Yun04kaGasai/Command-Case-1-Guidance-System-Module-2098/Assets/Diagramma dejstvij bloka posledovatel'nogo vypolneniya tipov skanirovaniya.png

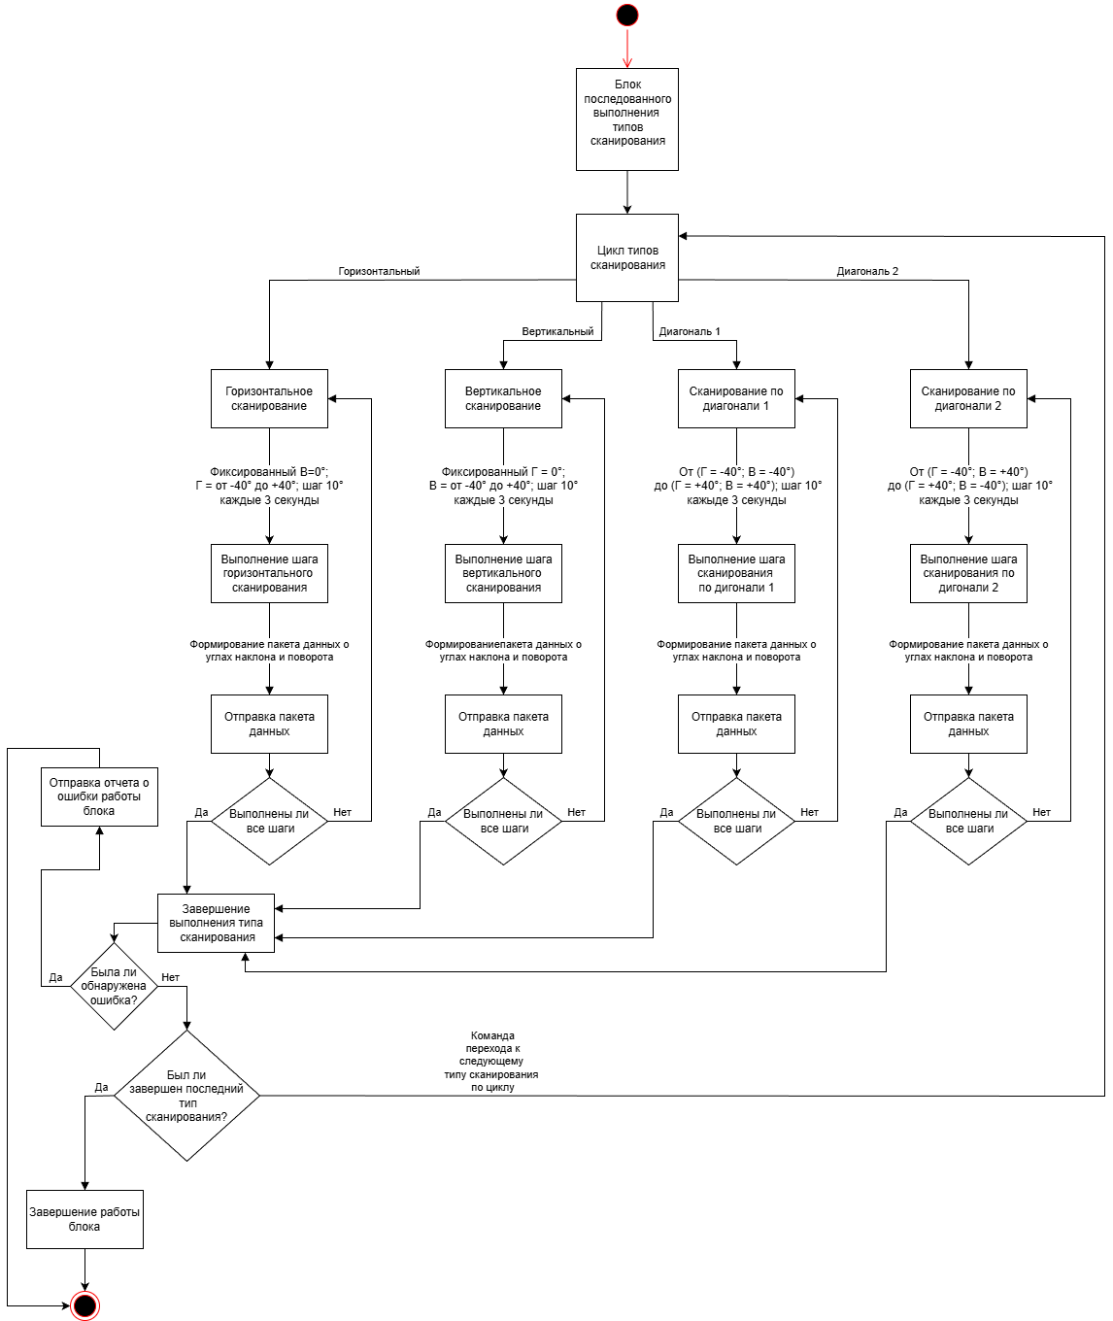
Assets/Diagramma dejstvij bloka posledovatel'nogo vypolneniya tipov skanirovaniya.png
