Yun04kaGasai/Command-Case-1-Guidance-System-Module-2098/Assets/Diagramma dejstvij CubeSat.png

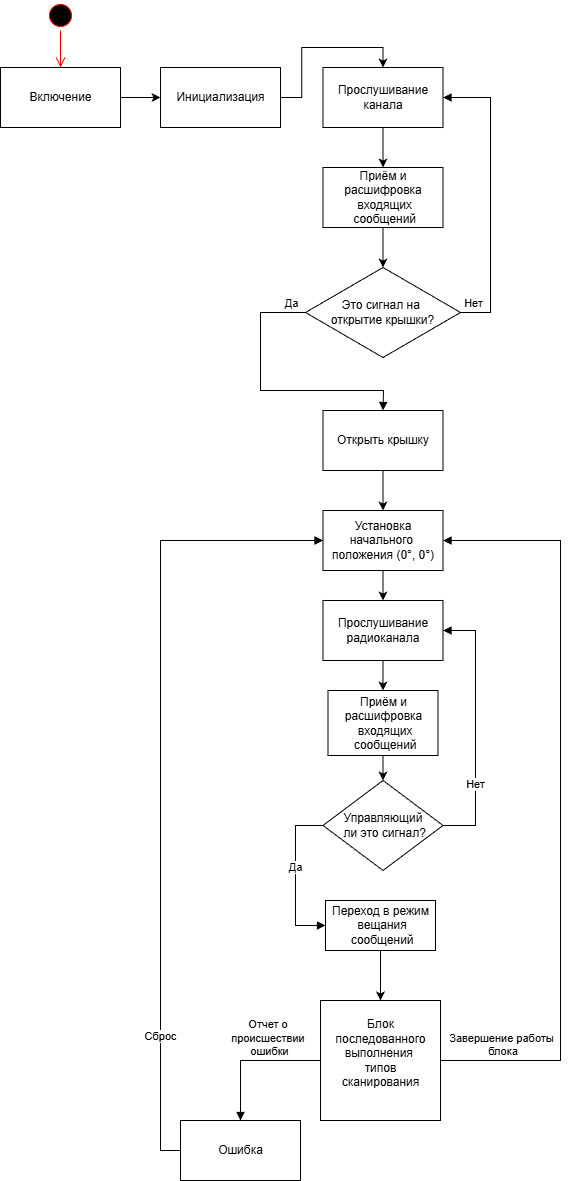
Assets/Diagramma dejstvij CubeSat.png
