Yun04kaGasai/Command-Case-1-Guidance-System-Module-2098/Assets/Diagramma klassov CubeSat.png

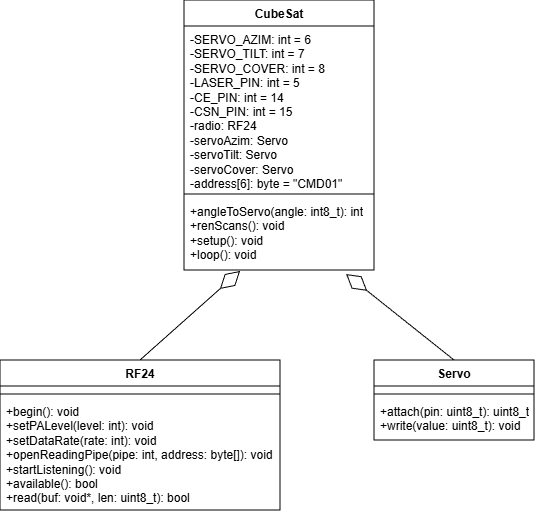
Assets/Diagramma klassov CubeSat.png
