Yun04kaGasai/Command-Case-1-Guidance-System-Module-2098/Assets/Diagramma klassov nazemnoj stancii.png

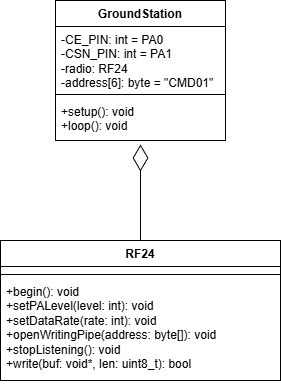
Assets/Diagramma klassov nazemnoj stancii.png
