Yun04kaGasai/Command-Case-1-Guidance-System-Module-2098/Assets/isometry razn.png

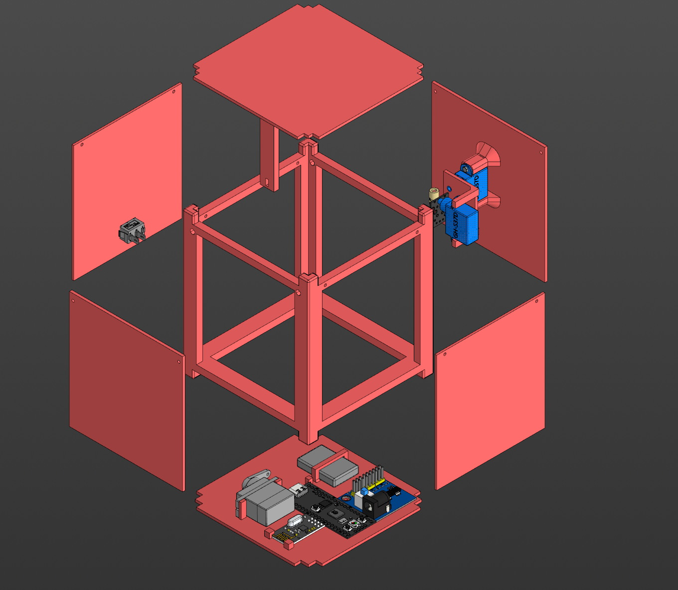
Assets/isometry razn.png
