Yun04kaGasai/Command-Case-1-Guidance-System-Module-2098/Assets/isometry.png

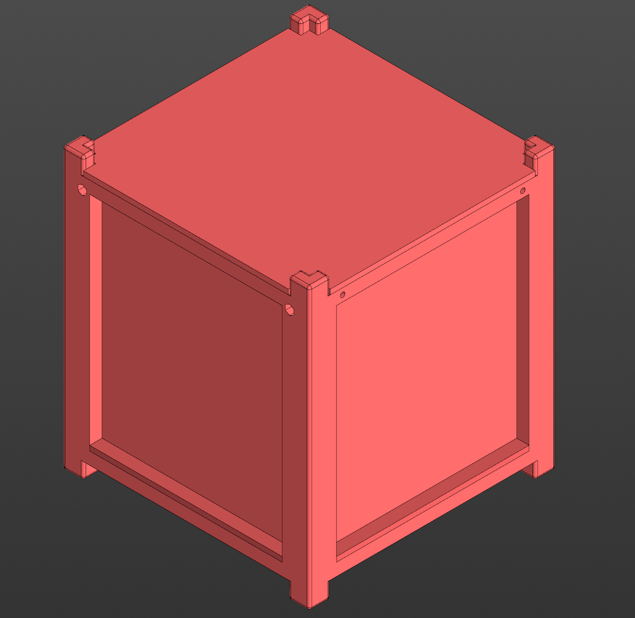
Assets/isometry.png
