Yun04kaGasai/Command-Case-1-Guidance-System-Module-2098/Assets/Potencial'naya skhema CubeSat.png

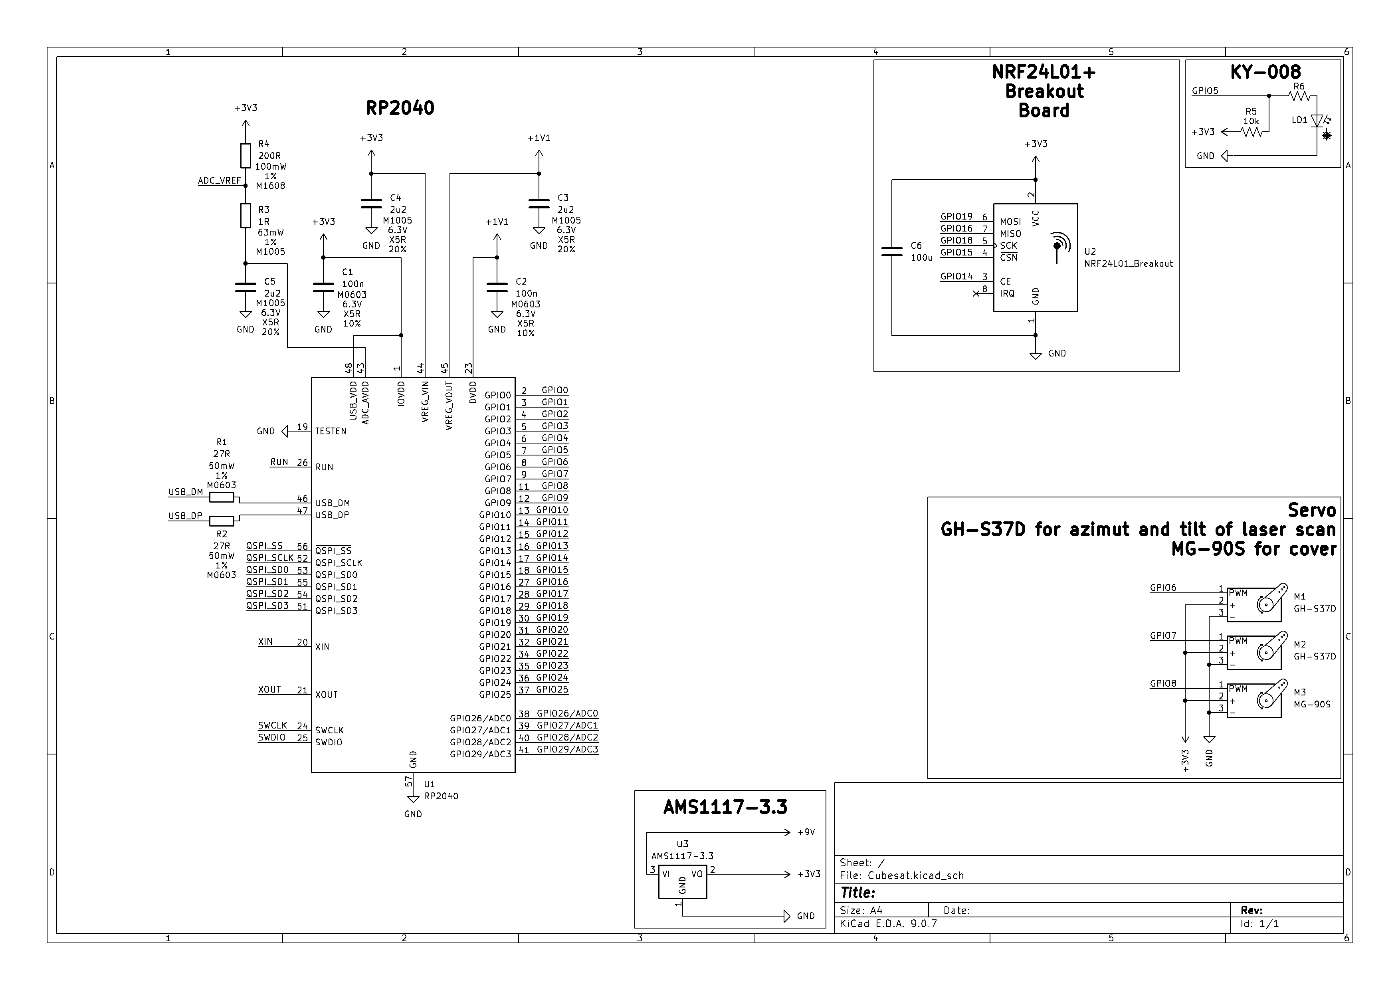
Assets/Potencial'naya skhema CubeSat.png
