Yun04kaGasai/Command-Case-1-Guidance-System-Module-2098/Assets/Potencial'naya skhema nazemnoj stancii.png

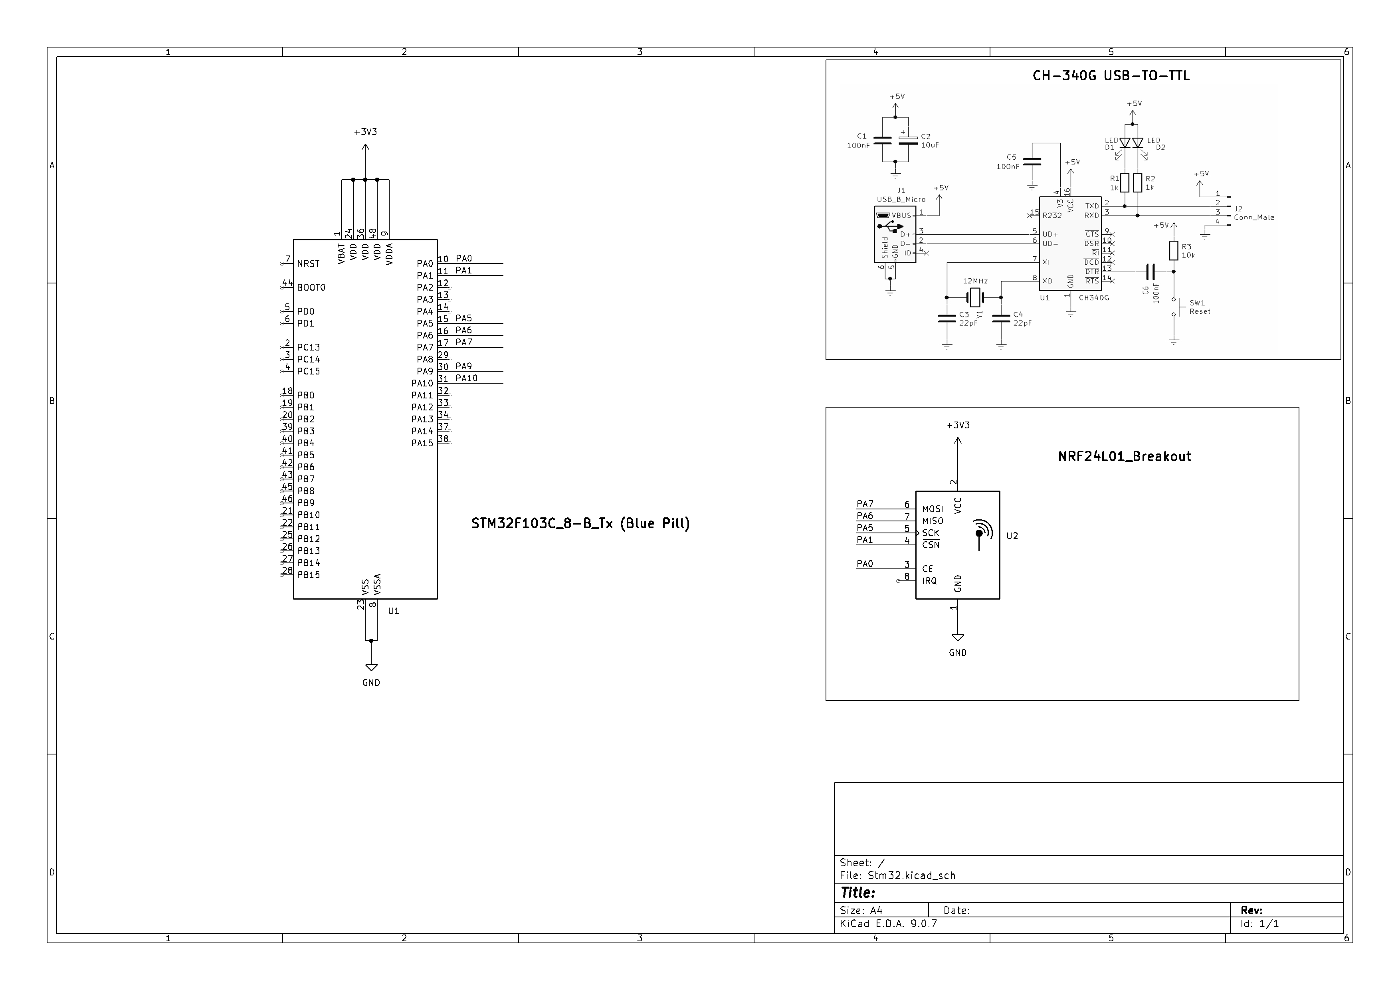
Assets/Potencial'naya skhema nazemnoj stancii.png
