Yun04kaGasai/Command-Case-1-Guidance-System-Module-2098/Assets/Сборка/Сборка.png

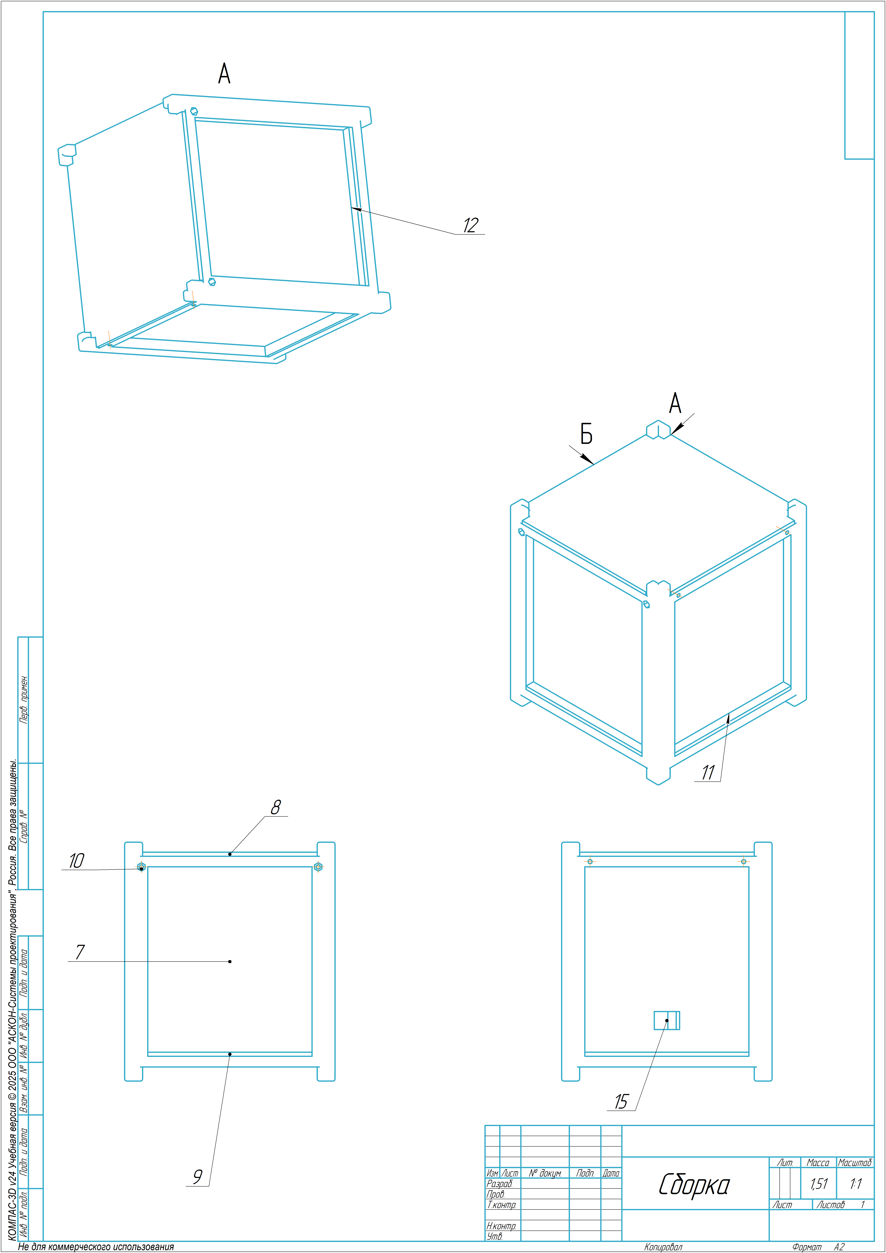
Assets/Сборка/Сборка.png
