Yun04kaGasai/Command-Case-1-Guidance-System-Module-2098/Assets/Чертежи/Дно кубсат.png

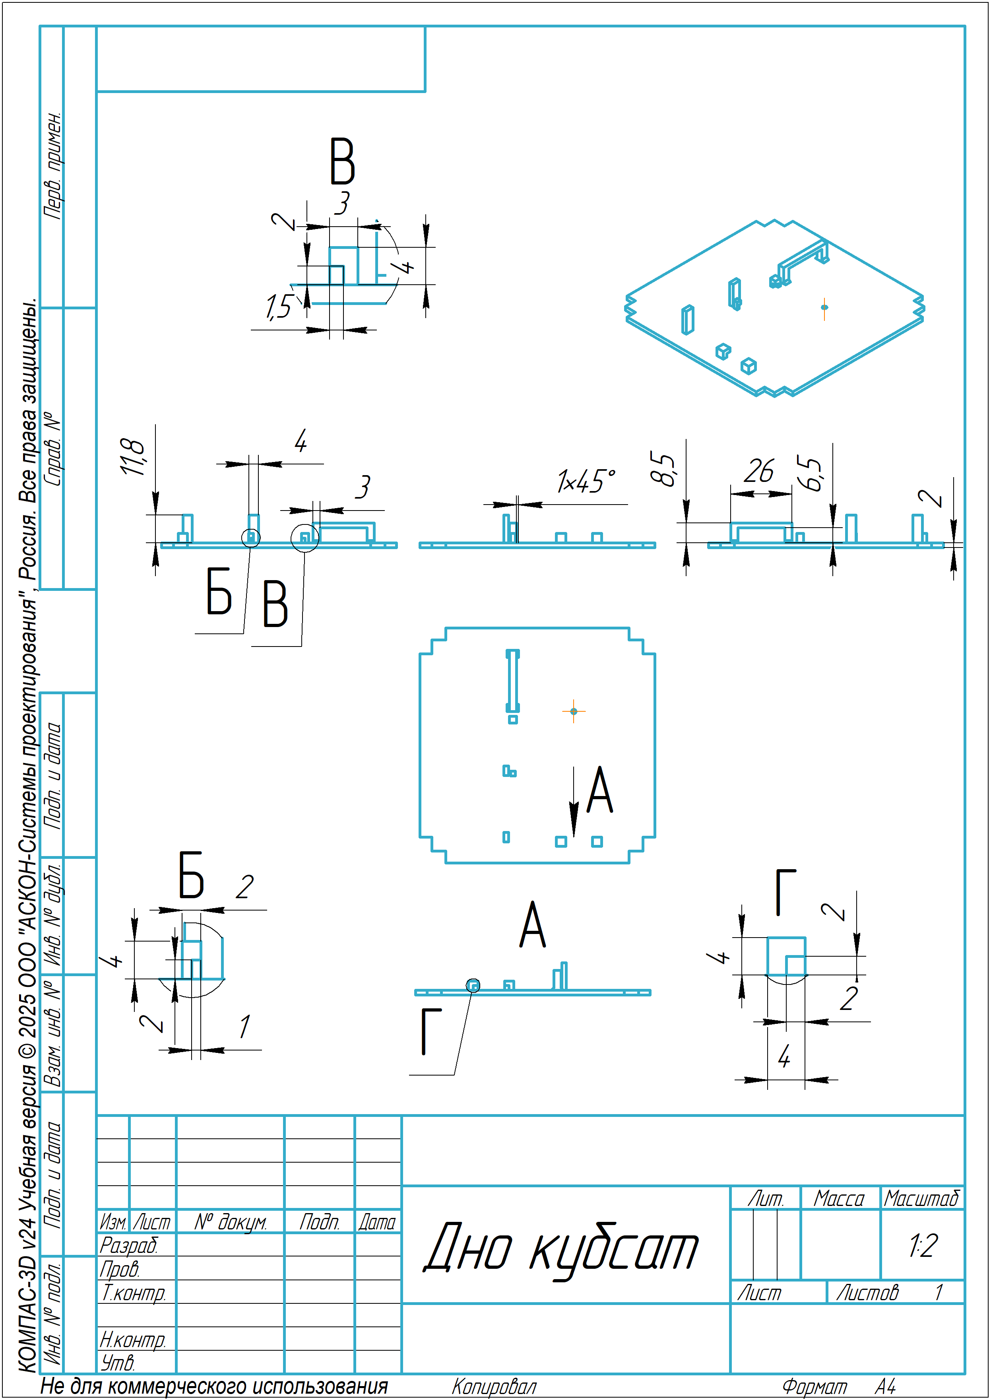
Assets/Чертежи/Дно кубсат.png
