Yun04kaGasai/Command-Case-1-Guidance-System-Module-2098/Assets/Чертежи/Крепление сервопривода.png

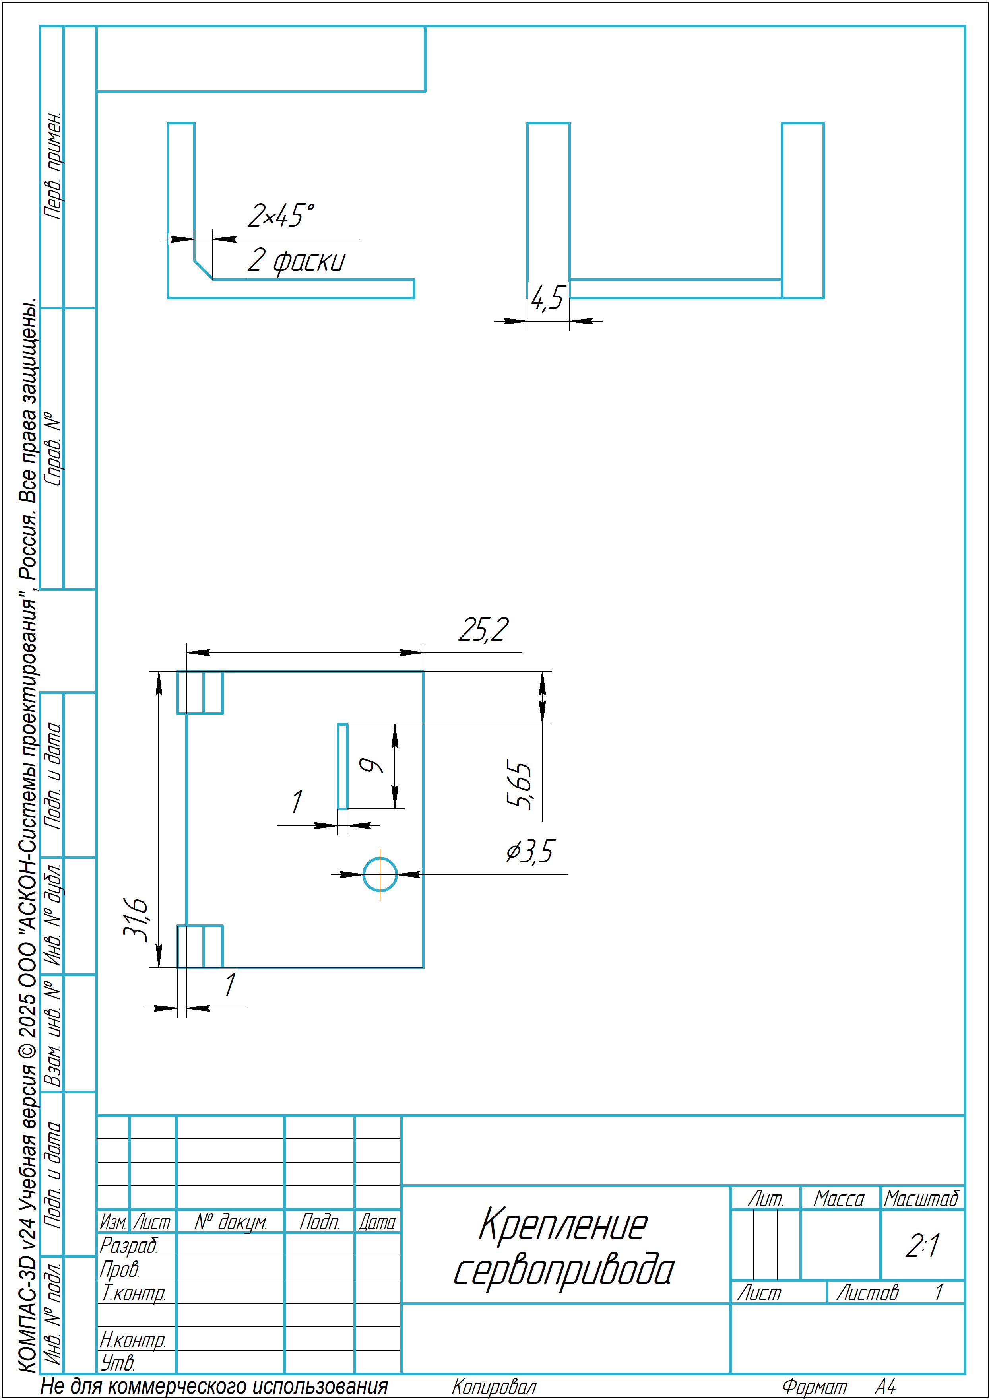
Assets/Чертежи/Крепление сервопривода.png
