Yun04kaGasai/Command-Case-1-Guidance-System-Module-2098/Assets/Чертежи/Стенка без крепления.png

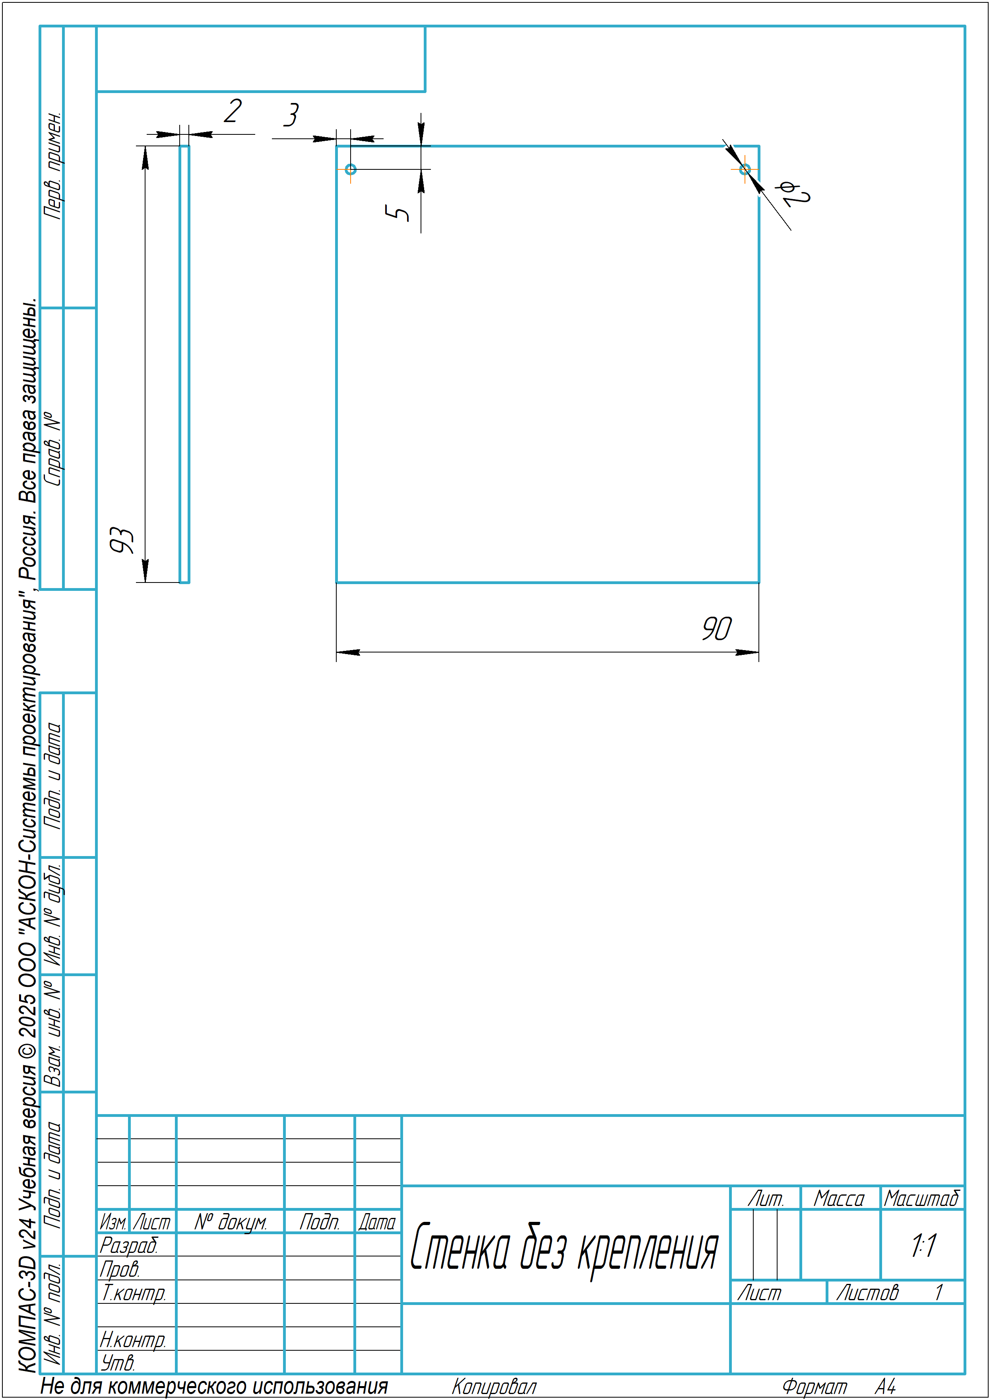
Assets/Чертежи/Стенка без крепления.png
