Yun04kaGasai/Command-Case-1-Guidance-System-Module-2098/Assets/Чертежи/Стенка_С_Креплением.png

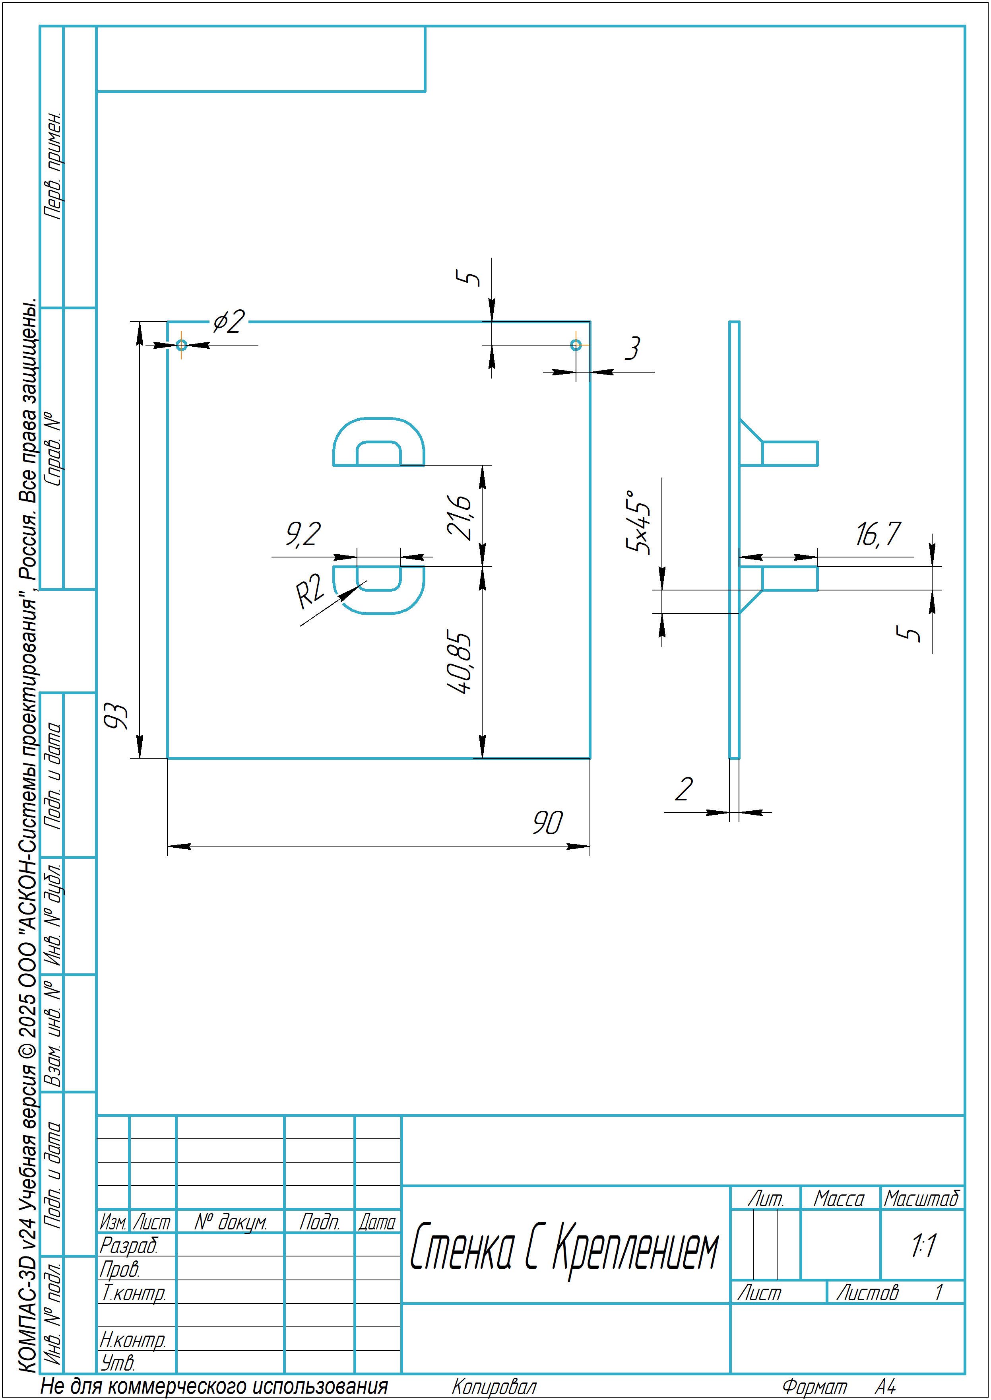
Assets/Чертежи/Стенка_С_Креплением.png
