Yun04kaGasai/Command-Case-1-Guidance-System-Module-2098/Assets/Сборка/RP2040/Rp2040 Type C.stl

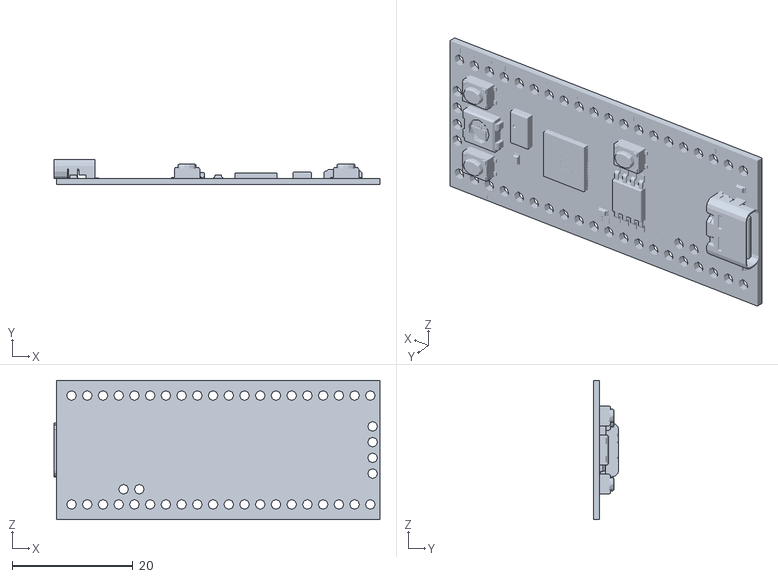
[picture p34: CAD file, 2026-01-14]
Assets/Сборка/RP2040/Rp2040 Type C.stl
53.9 x 4.19 x 23.0
