Yun04kaGasai/Command-Case-1-Guidance-System-Module-2098/Assets/Сборка/RadioFrequencyCommunicationModule_nRF24L01.STEP

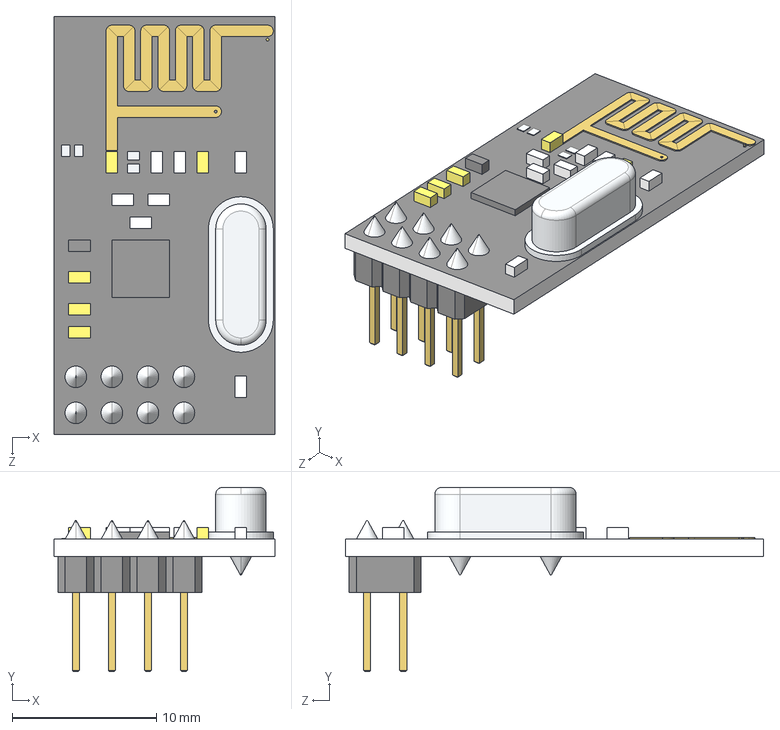
[picture p35: CAD file, 2026-01-14]
Assets/Сборка/RadioFrequencyCommunicationModule_nRF24L01.STEP
15.3 x 12.8 x 29.0 mm
