Yun04kaGasai/Command-Case-1-Guidance-System-Module-2098/Assets/Сборка/RP2040/C-Type Female - 6-Pin SMD.step

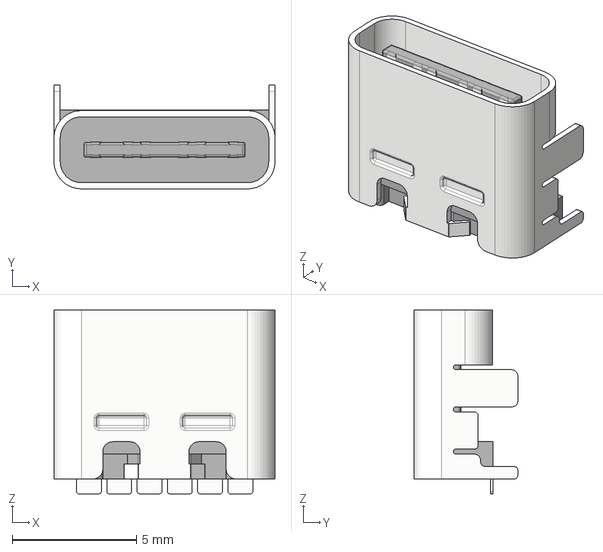
[picture p36: CAD file, 2026-01-14]
Assets/Сборка/RP2040/C-Type Female - 6-Pin SMD.step
8.90 x 4.18 x 7.40 mm
