Yun04kaGasai/Command-Case-1-Guidance-System-Module-2098/3D-модели/Крышка.stp

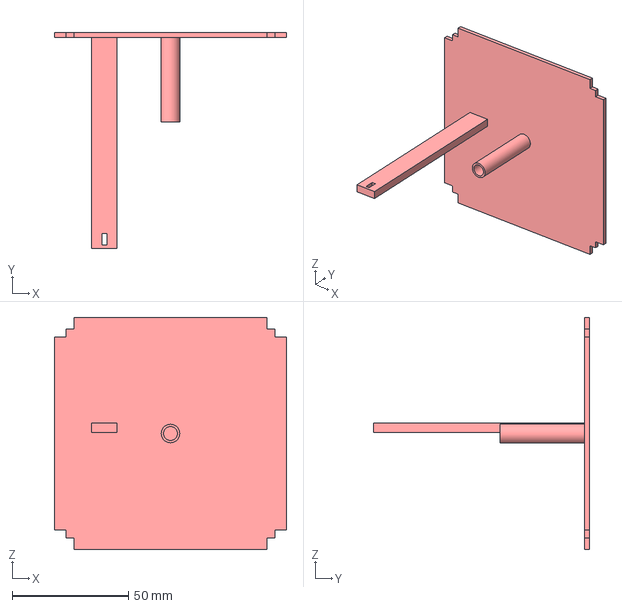
[picture p37: CAD file, 2026-01-18]
3D-модели/Крышка.stp
100.0 x 93.0 x 100.0 mm
