Yun04kaGasai/Command-Case-1-Guidance-System-Module-2098/Assets/Сборка/Сборка Кубсат.stp

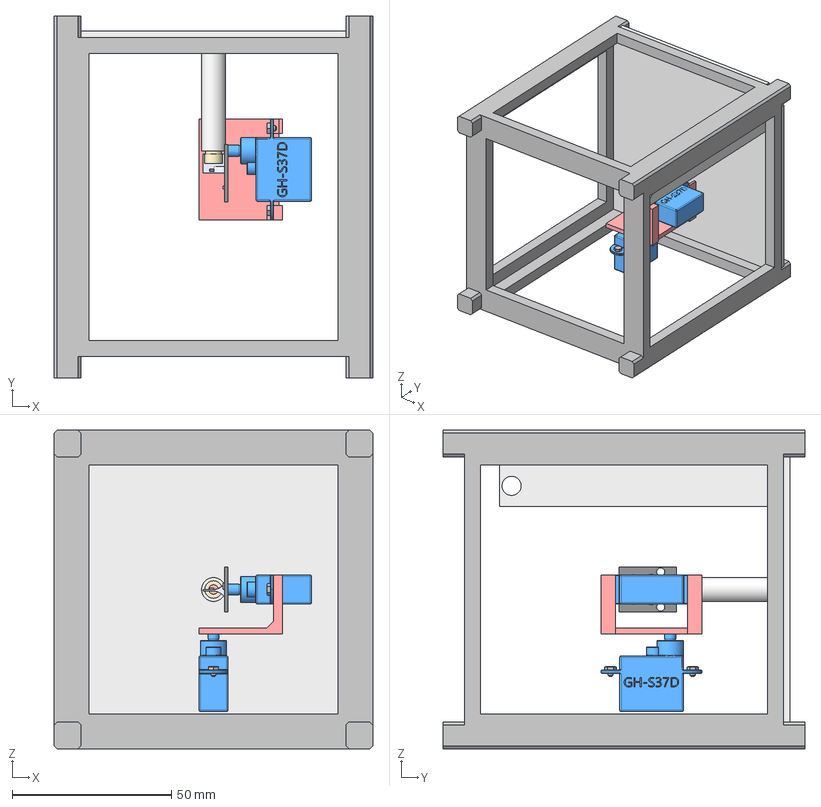
[picture p38: CAD file, 2026-01-14]
Assets/Сборка/Сборка Кубсат.stp
100.0 x 113.5 x 100.0 mm
Gh-S37D Servo x 2
KY-008
