Yun04kaGasai/Command-Case-1-Guidance-System-Module-2098/3D-модели/Крепление сервопривода.stp

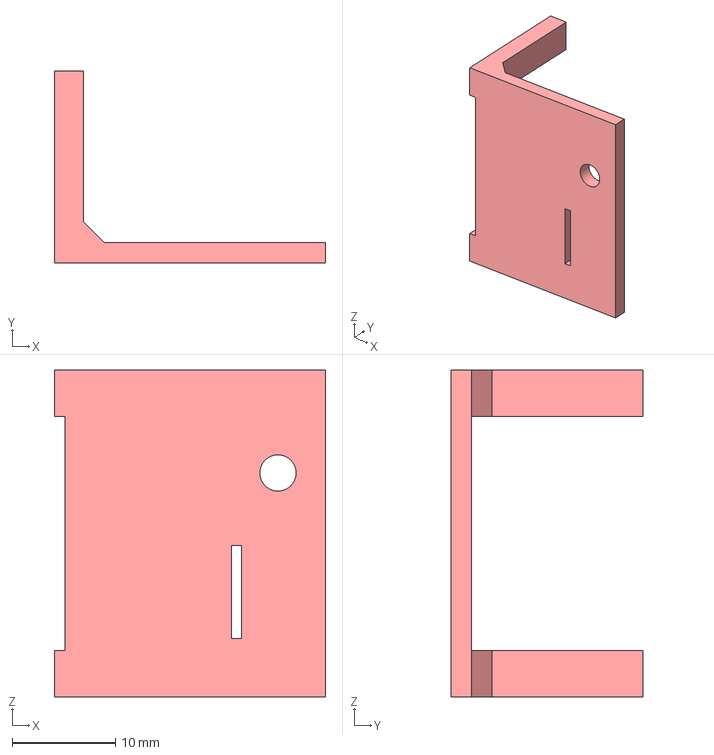
[picture p39: CAD file, 2026-01-18]
3D-модели/Крепление сервопривода.stp
26.2 x 18.6 x 31.6 mm
