Yun04kaGasai/Command-Case-1-Guidance-System-Module-2098/Assets/Сборка/MG90S ARM.step

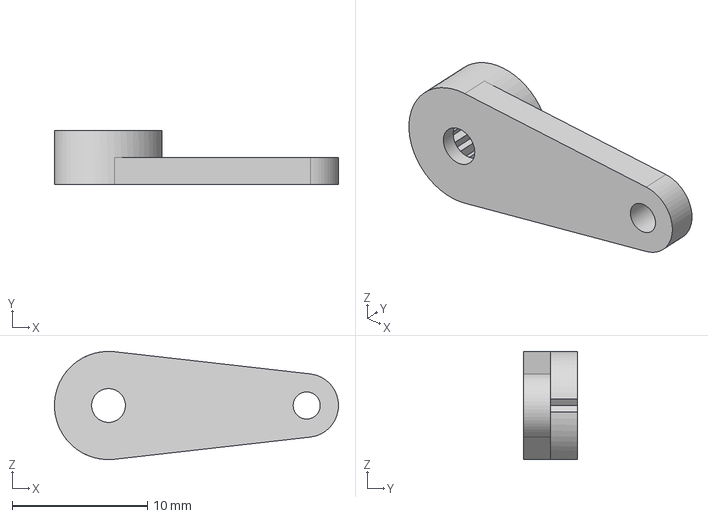
[picture p40: CAD file, 2026-01-14]
Assets/Сборка/MG90S ARM.step
21.0 x 4.00 x 8.00 mm
