Yun04kaGasai/Command-Case-1-Guidance-System-Module-2098/Assets/Сборка/DC_Power_Jack_PCB_Mounted_2.1mm.step

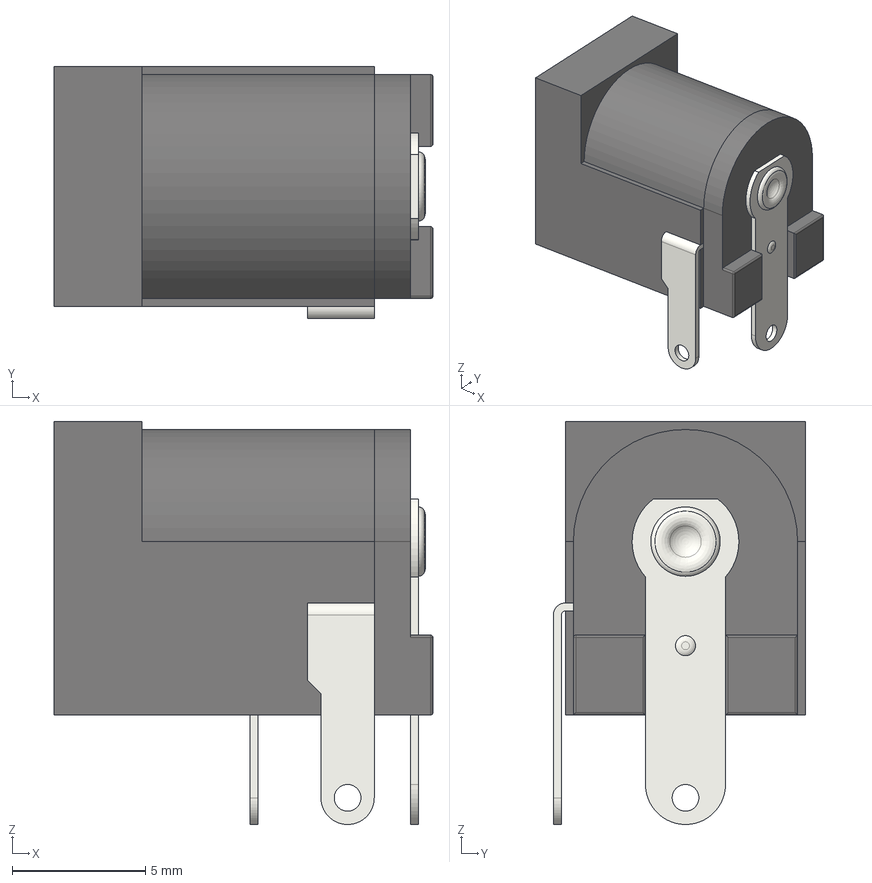
[picture p41: CAD file, 2026-01-14]
Assets/Сборка/DC_Power_Jack_PCB_Mounted_2.1mm.step
14.2 x 9.45 x 15.1 mm
Plastic_Body_1of2
Plastic_Body_2of2
PIN_01
PIN_03
PIN_02
Boner
